sam0910/narmi000/CASE-3D/render/Ultrasonic-3.png

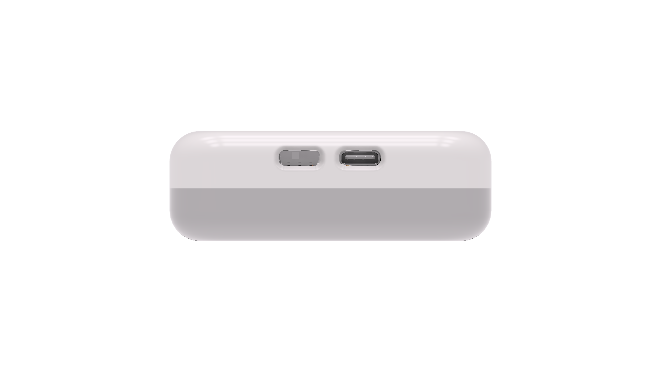
CASE-3D/render/Ultrasonic-3.png
