sam0910/narmi000/PCB/material-estimates/증빙자료/제외부품.png

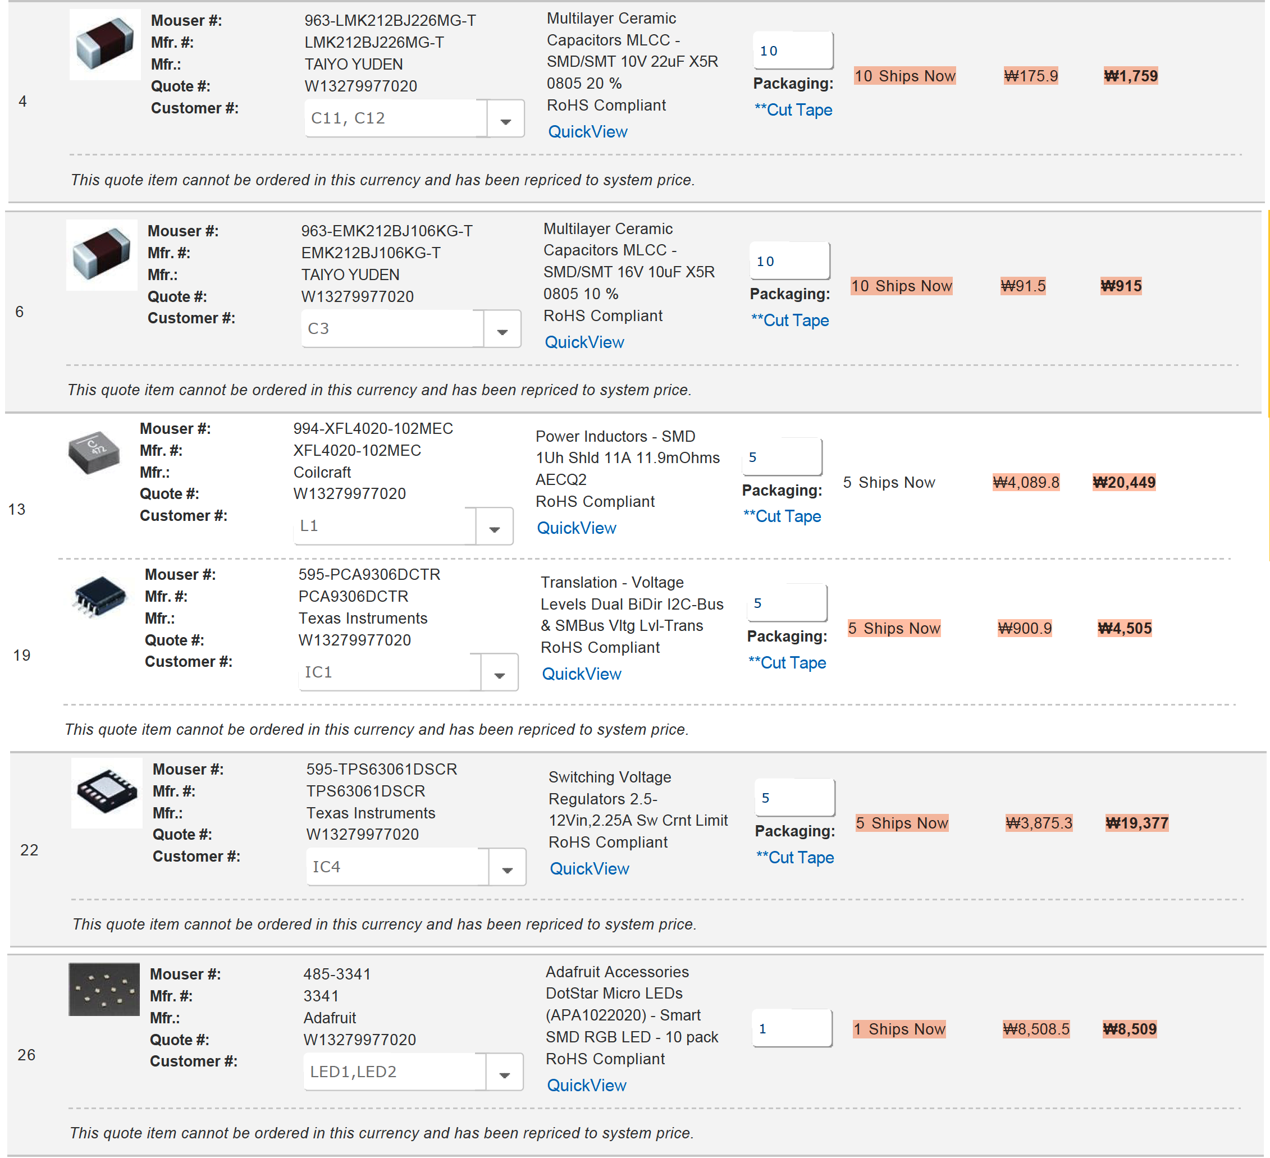
PCB/material-estimates/증빙자료/제외부품.png
