sam0910/narmi000/src/app/sensor/sht40/crc_mod.py

"""
MIT License
Copyright (c) 2022 Roman Shevchik

CRC calculation implementation
 8 bit
 polynomial 0x31 (x^8 + x^5 + x^4 + 1)
 initial value 0xFF
 input reflection: no
 output reflection: no
 final XOR: no

 CRC-8 Examples:
    Input sequence: 0x01 0x02 0x03
    CRC-8: 0x87
    Input sequence: 0 1 2 3 4 5 6 7 8 9
    CRC-8: 0x52
"""


def crc8(sequence: bytes, polynomial: int, init_value: int = 0x00, final_xor=0x00):
    mask = 0xFF
    crc = init_value & mask
    for item in sequence:
        crc ^= item & mask
        for _ in range(8):
            if crc & 0x80:
                crc = mask & ((crc << 1) ^ polynomial)
            else:
                crc = mask & (crc << 1)
    return crc ^ final_xor
